LeafCutterLabs/miniMACRO5/photos/finish3.jpg

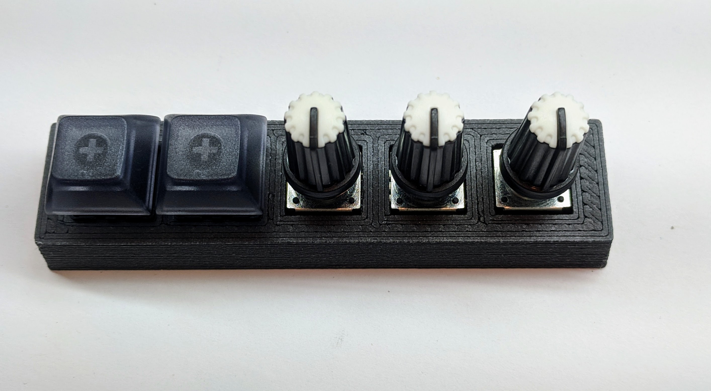
photos/finish3.jpg
