LeafCutterLabs/miniMACRO5/photos/finish4.jpg

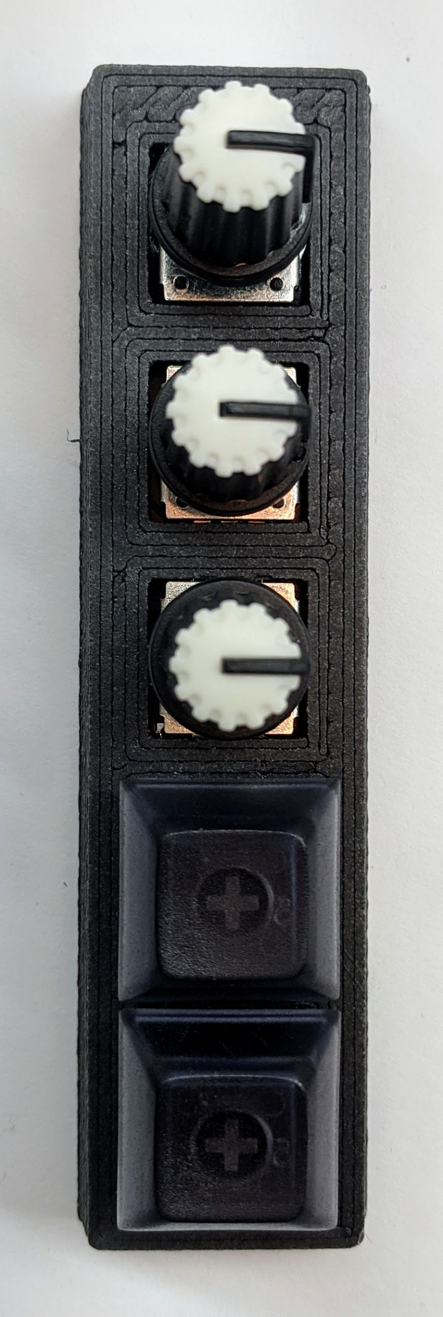
photos/finish4.jpg
