LeafCutterLabs/miniMACRO5/photos/finishedshow.jpg

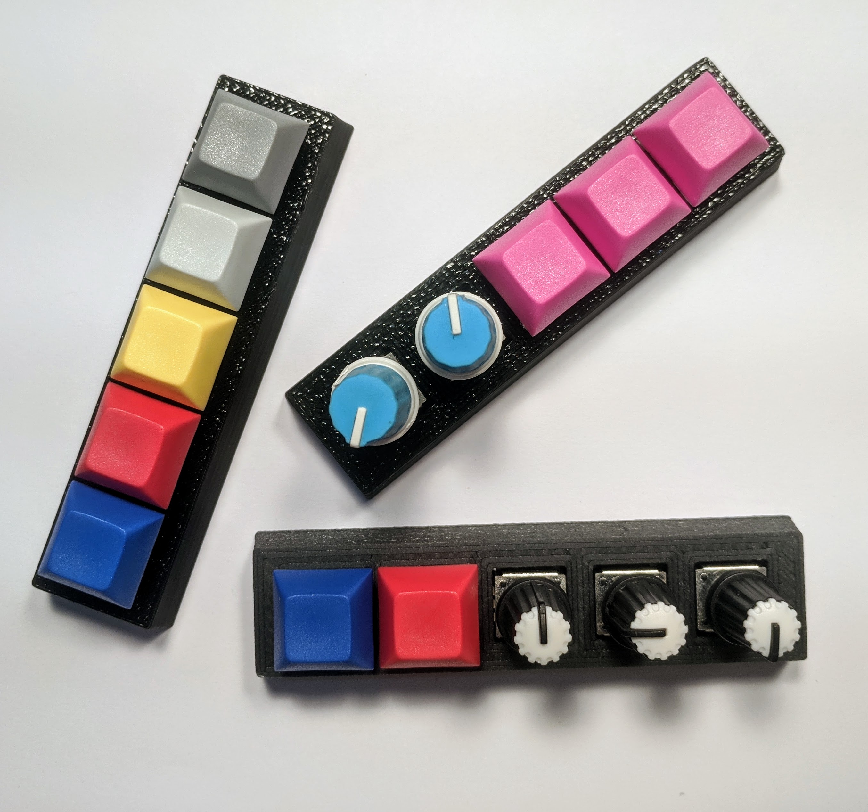
photos/finishedshow.jpg
