LeafCutterLabs/miniMACRO5/photos/promicro.jpg

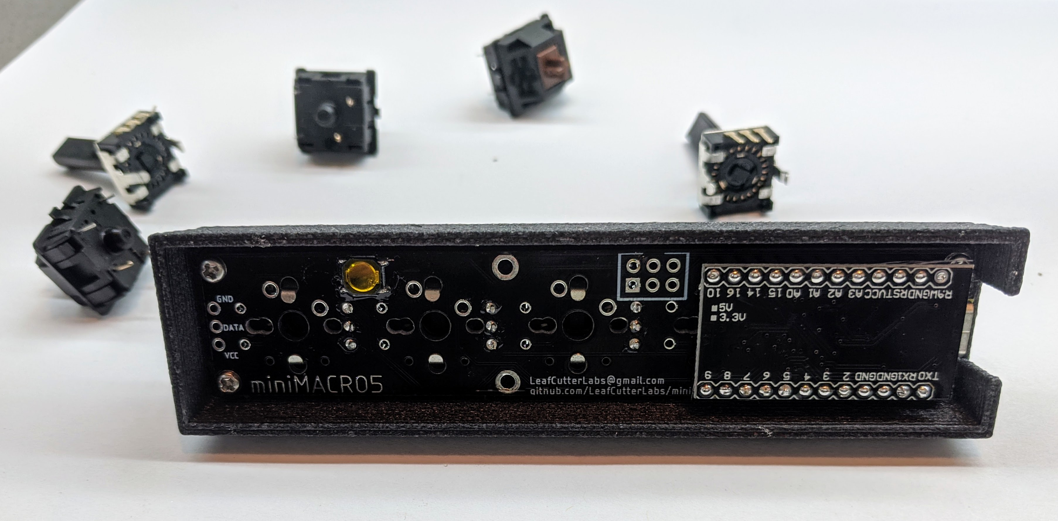
photos/promicro.jpg
