LeafCutterLabs/miniMACRO5/photos/rotaries.jpg

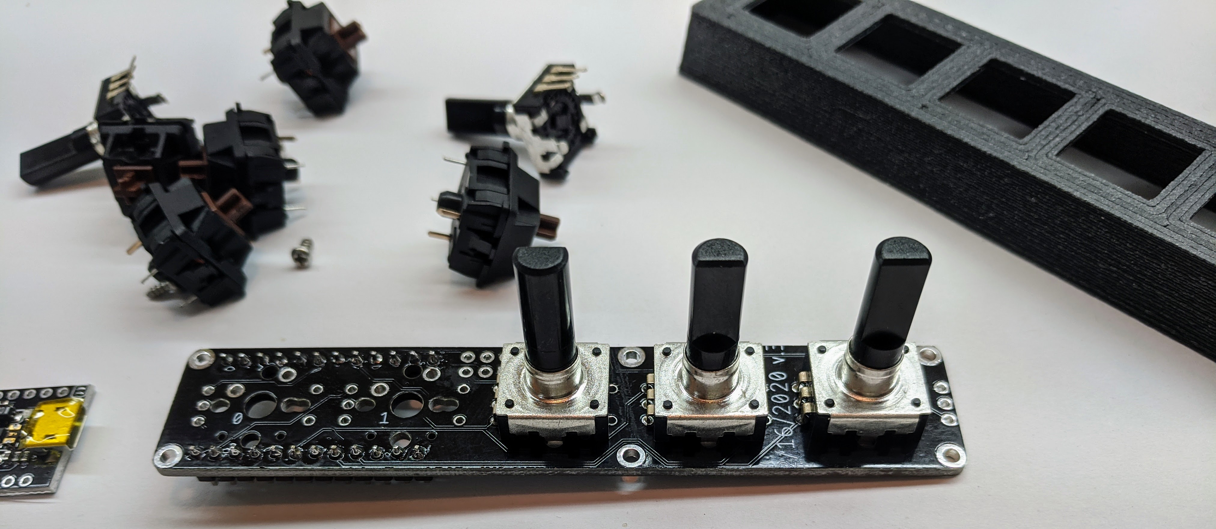
photos/rotaries.jpg
