LeafCutterLabs/miniMACRO5/photos/tape.jpg

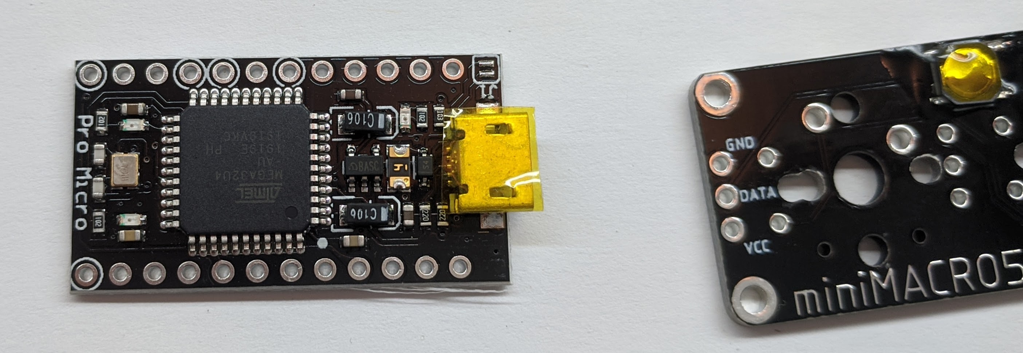
photos/tape.jpg
