LeafCutterLabs/miniMACRO5/photos/v3.jpg

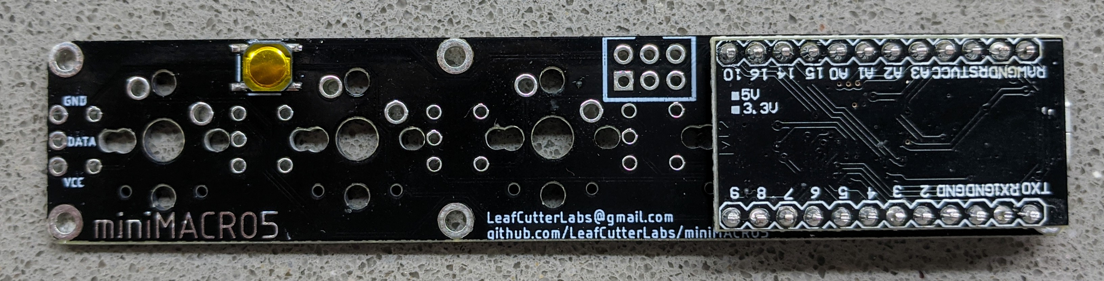
photos/v3.jpg
